RedDuckBot/Mouse-Droid/3D_print_files/custom_parts/top_disco_dome_cover.stl

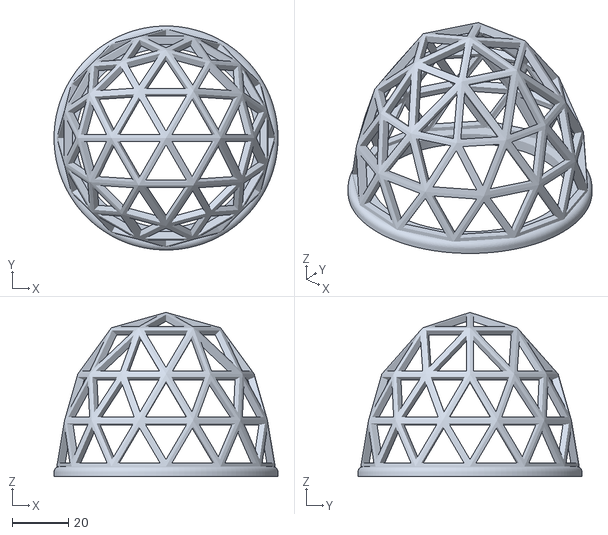
[picture p17: CAD file, 2024-07-10]
3D_print_files/custom_parts/top_disco_dome_cover.stl
80.0 x 80.0 x 58.7
