RedDuckBot/Mouse-Droid/3D_print_files/original_parts/MSE_base_6to10.stl

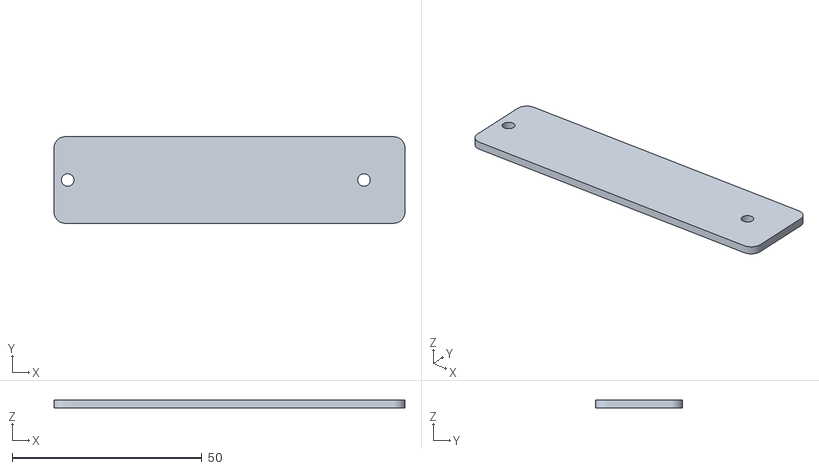
[picture p18: CAD file, 2024-07-10]
3D_print_files/original_parts/MSE_base_6to10.stl
92.4 x 22.8 x 2.10
