RedDuckBot/Mouse-Droid/3D_print_files/custom_parts/top_disco_platform.stl

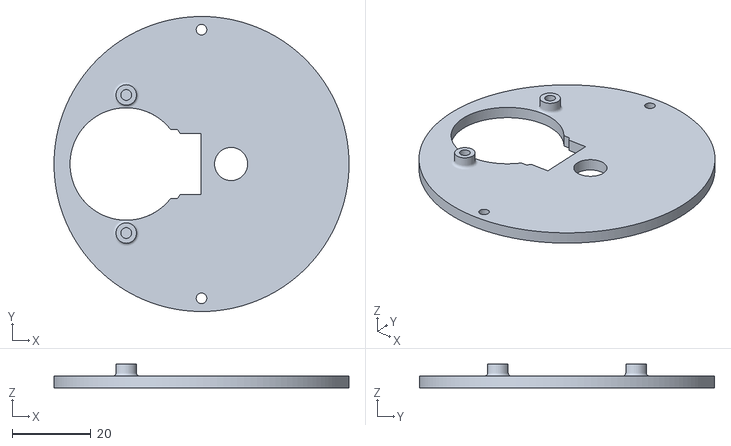
[picture p19: CAD file, 2024-07-10]
3D_print_files/custom_parts/top_disco_platform.stl
74.8 x 74.8 x 5.96
