RedDuckBot/Mouse-Droid/3D_print_files/original_parts/MSE_Lower_Portion6to10.stl

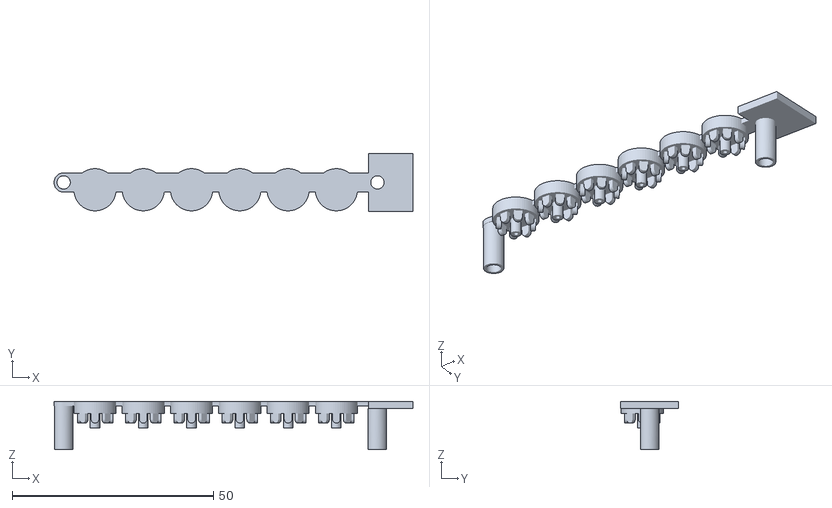
[picture p20: CAD file, 2024-07-10]
3D_print_files/original_parts/MSE_Lower_Portion6to10.stl
89.2 x 14.4 x 12.0
