RedDuckBot/Mouse-Droid/3D_print_files/original_parts/Front_Tire.stl

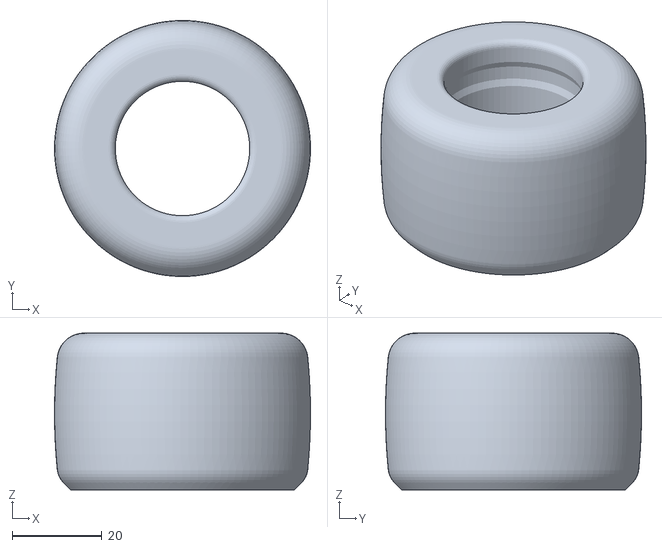
[picture p21: CAD file, 2024-07-10]
3D_print_files/original_parts/Front_Tire.stl
57.2 x 57.2 x 35.0
