RedDuckBot/Mouse-Droid/droid_setup/ros2_ws/src/droid_server_commands/src/DYPlayer.cpp

/**
 * Abstraction of basic features of the DY-SV17F mp3 player board, written for
 * Arduino, should work on other frameworks as well. Instead of DY-SV17F I will
 * from here on refer to it as the "module".
 *
 * There are some virtual methods that MUST be overridden (serialRead and
 * serialWrite) and one that you may override (begin)
 */

//Code obtained for this file from https://github.com/SnijderC/dyplayer

#include <ctype.h>
#include <string.h>
#include "sound_module/DYPlayer.hpp"

namespace DY
{
  void DYPlayer::serialWrite(uint8_t byte)
  {
    uint8_t buffer[1] = {byte};
    serialWrite(buffer, 1);
  }

  uint8_t inline DYPlayer::checksum(uint8_t *data, uint8_t len)
  {
    uint8_t sum = 0;
    for (uint8_t i = 0; i < len; i++)
    {
      sum = sum + data[i];
    }
    return sum;
  }

  bool inline DYPlayer::validateCrc(uint8_t *data, uint8_t len)
  {
    uint8_t crc = data[len - 1];
    return checksum(data, len - 1) == crc;
  }

  void DYPlayer::sendCommand(uint8_t *data, uint8_t len)
  {
    uint8_t crc = checksum(data, len);
    serialWrite(data, len);
    serialWrite(crc);
  }

  void DYPlayer::sendCommand(uint8_t *data, uint8_t len, uint8_t crc)
  {
    serialWrite(data, len);
    serialWrite(crc);
  }

  bool DYPlayer::getResponse(uint8_t *buffer, uint8_t len)
  {
    if (serialRead(buffer, len) > 0)
    {
      if (validateCrc(buffer, len))
      {
        return true;
      }
    }
    return false;
  }

  void DYPlayer::byPathCommand(uint8_t command, device_t device, char *path)
  {
    uint8_t len = strlen(path);
    if (len < 1)
      return;
    uint8_t _len = len;
    // Count / in path and, except root slash and determine new length
    for (uint8_t i = 1; i < len; i++)
    {
      if (path[i] == '/')
        _len++;
    }
#ifdef DY_PATHS_IN_HEAP
    uint8_t *_command = new uint8_t[_len + 4];
#else
    uint8_t _command[DY_PATH_LEN + 4];
#endif

    _command[0] = 0xaa;
    _command[1] = command;
    _command[2] = _len + 1;
    _command[3] = (uint8_t)device;
    _command[4] = path[0];
    uint8_t j = 5;
    for (uint8_t i = 1; i < len; i++)
    {
      switch (path[i])
      {
      case '.':
        _command[j] = '*';
        break;
      case '/':
        _command[j] = '*';
        j++;
        // fall-through
      default:
        _command[j] = toupper(path[i]);
      }
      j++;
    }
    sendCommand(_command, _len + 4);
#ifdef DY_PATHS_IN_HEAP
    delete[] _command;
#endif
  }

  play_state_t DYPlayer::checkPlayState()
  {
    uint8_t command[3] = {0xaa, 0x01, 0x00};
    sendCommand(command, 3, 0xab);
    uint8_t buffer[5];
    if (getResponse(buffer, 5))
    {
      return (play_state_t)buffer[3];
    }
    return PlayState::Fail;
  }

  void DYPlayer::play()
  {
    uint8_t command[3] = {0xaa, 0x02, 0x00};
    sendCommand(command, 3, 0xac);
  }

  void DYPlayer::pause()
  {
    uint8_t command[3] = {0xaa, 0x03, 0x00};
    sendCommand(command, 3, 0xad);
  }

  void DYPlayer::stop()
  {
    uint8_t command[3] = {0xaa, 0x04, 0x00};
    sendCommand(command, 3, 0xae);
  }

  void DYPlayer::previous()
  {
    uint8_t command[3] = {0xaa, 0x05, 0x00};
    sendCommand(command, 3, 0xaf);
  }

  void DYPlayer::next()
  {
    uint8_t command[3] = {0xaa, 0x06, 0x00};
    sendCommand(command, 3, 0xb0);
  }

  void DYPlayer::playSpecified(uint16_t number)
  {
    uint8_t command[5] = {0xaa, 0x07, 0x02, 0x00, 0x00};
    command[3] = number >> 8;
    command[4] = number & 0xff;
    sendCommand(command, 5);
  }
  void DYPlayer::playSpecifiedDevicePath(device_t device, char *path)
  {
    byPathCommand(0x08, device, path);
  }

  device_t DYPlayer::getPlayingDevice()
  {
    uint8_t command[3] = {0xaa, 0x0a, 0x00};
    sendCommand(command, 3, 0xb4);
    uint8_t buffer[5];
    if (getResponse(buffer, 5))
    {
      return (device_t)buffer[3];
    }
    return Device::Fail;
  }

  void DYPlayer::setPlayingDevice(device_t device)
  {
    uint8_t command[4] = {0xaa, 0x0b, 0x01, 0x00};
    command[3] = (uint8_t)device;
    sendCommand(command, 4);
  }

  uint16_t DYPlayer::getSoundCount()
  {
    uint8_t command[3] = {0xaa, 0x0c, 0x00};
    sendCommand(command, 3, 0xb6);
    uint8_t buffer[6];
    if (getResponse(buffer, 6))
    {
      return (buffer[3] << 8) | buffer[4];
    }
    return 0;
  }

  uint16_t DYPlayer::getPlayingSound()
  {
    uint8_t command[3] = {0xaa, 0x0d, 0x00};
    sendCommand(command, 3, 0xb7);
    uint8_t buffer[6];
    if (getResponse(buffer, 6))
    {
      return (buffer[3] << 8) | buffer[4];
    }
    return 0;
  }

  void DYPlayer::previousDir(playDirSound_t song)
  {
    if (song == PreviousDir::LastSound)
    {
      uint8_t command[3] = {0xaa, 0x0e, 0x00};
      sendCommand(command, 3, 0xb8);
    }
    else
    {
      uint8_t command[3] = {0xaa, 0x0f, 0x00};
      sendCommand(command, 3, 0xb9);
    }
  }

  uint16_t DYPlayer::getFirstInDir()
  {
    uint8_t command[3] = {0xaa, 0x11, 0x00};
    sendCommand(command, 3, 0xbb);
    uint8_t buffer[6];
    if (getResponse(buffer, 6))
    {
      return (buffer[3] << 8) | buffer[4];
    }
    return 0;
  }

  uint16_t DYPlayer::getSoundCountDir()
  {
    uint8_t command[3] = {0xaa, 0x12, 0x00};
    sendCommand(command, 3, 0xbc);
    uint8_t buffer[6];
    if (getResponse(buffer, 6))
    {
      return (buffer[3] << 8) | buffer[4];
    }
    return 0;
  }

  void DYPlayer::setVolume(uint8_t volume)
  {
    uint8_t command[4] = {0xaa, 0x13, 0x01, 0x00};
    command[3] = volume;
    sendCommand(command, 4);
  }

  void DYPlayer::volumeIncrease()
  {
    uint8_t command[3] = {0xaa, 0x14, 0x00};
    sendCommand(command, 3, 0xbe);
  }

  void DYPlayer::volumeDecrease()
  {
    uint8_t command[3] = {0xaa, 0x15, 0x00};
    sendCommand(command, 3, 0xbf);
  }

  void DYPlayer::interludeSpecified(device_t device, uint16_t number)
  {
    uint8_t command[6] = {0xaa, 0x0b, 0x03, 0x00, 0x00, 0x00};
    command[3] = (uint8_t)device;
    command[4] = number >> 8;
    command[5] = number & 0xff;
    sendCommand(command, 6);
  }

  void DYPlayer::interludeSpecifiedDevicePath(device_t device, char *path)
  {
    byPathCommand(0x17, device, path);
  }

  void DYPlayer::stopInterlude()
  {
    uint8_t command[3] = {0xaa, 0x10, 0x00};
    sendCommand(command, 3, 0xba);
  }

  void DYPlayer::setCycleMode(play_mode_t mode)
  {
    uint8_t command[4] = {0xaa, 0x18, 0x01, 0x00};
    command[3] = mode;
    sendCommand(command, 4);
  }
  void DYPlayer::setCycleTimes(uint16_t cycles)
  {
    uint8_t command[5] = {0xaa, 0x19, 0x02, 0x00, 0x00};
    command[3] = cycles >> 8;
    command[4] = cycles & 0xff;
    sendCommand(command, 5);
  }

  void DYPlayer::setEq(eq_t eq)
  {
    uint8_t command[4] = {0xaa, 0x1a, 0x01, 0x00};
    command[3] = (uint8_t)eq;
    sendCommand(command, 4);
  }

  void DYPlayer::select(uint16_t number)
  {
    uint8_t command[5] = {0xaa, 0x1f, 0x02, 0x00, 0x00};
    command[3] = number >> 8;
    command[4] = number & 0xff;
    sendCommand(command, 5);
  }
  void DYPlayer::combinationPlay(char *sounds[], uint8_t len)
  {
    if (len < 1)
      return;
    // This part of the command can be easily determined already.
    uint8_t command[3] = {0xaa, 0x1b, 0x00};
    command[2] = len * 2;
    // Depends on the length, checksum is a sum so we can add the other values
    // later.
    uint8_t crc = checksum(command, 3);
    // Send the command and length already.
    serialWrite(command, 3);
    // Send each pair of chars containing the file name and add the values of
    // each char to the crc.
    for (uint8_t i = 0; i < len; i++)
    {
      crc += checksum((uint8_t *)sounds[i], 2);
      serialWrite((uint8_t *)sounds[i], 2);
    }
    // Lastly, write the crc value.
    serialWrite(crc);
  }

  void DYPlayer::endCombinationPlay()
  {
    uint8_t command[3] = {0xaa, 0x1c, 0x00};
    sendCommand(command, 3, 0xc6);
  }
}
