RedDuckBot/Mouse-Droid/droid_setup/ros2_ws/src/droid_server_commands/src/PullDirection.cpp

#include "libgpio/PullDirection.hpp"

#include <stdexcept>

//File taken from repo: https://github.com/buildrobotsbetter/rpi4b_gpio-example
namespace libgpio
{

PullDirection::operator Value() const
{
    return value;
}

std::string PullDirection::toString() const
{
    switch (value)
    {
        case UP:
            return "UP";

        case DOWN:
            return "DOWN";

        case OFF:
            return "OFF";
    }

    throw std::runtime_error("Could convert PullDirection to string");
}

} // namespace libgpio
